Mircerson/AERQ/Code/v1/stm32customtargets/TARGET_STM32F4/TARGET_CORE2/PeripheralPinMaps.h

/* mbed Microcontroller Library
 *******************************************************************************
 * Copyright (c) 2018, STMicroelectronics
 * All rights reserved.
 *
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
 * THIS SOFTWARE IS PROVIDED BY THE COPYRIGHT HOLDERS AND CONTRIBUTORS "AS IS"
 * AND ANY EXPRESS OR IMPLIED WARRANTIES, INCLUDING, BUT NOT LIMITED TO, THE
 * IMPLIED WARRANTIES OF MERCHANTABILITY AND FITNESS FOR A PARTICULAR PURPOSE ARE
 * DISCLAIMED. IN NO EVENT SHALL THE COPYRIGHT HOLDER OR CONTRIBUTORS BE LIABLE
 * FOR ANY DIRECT, INDIRECT, INCIDENTAL, SPECIAL, EXEMPLARY, OR CONSEQUENTIAL
 * DAMAGES (INCLUDING, BUT NOT LIMITED TO, PROCUREMENT OF SUBSTITUTE GOODS OR
 * SERVICES; LOSS OF USE, DATA, OR PROFITS; OR BUSINESS INTERRUPTION) HOWEVER
 * CAUSED AND ON ANY THEORY OF LIABILITY, WHETHER IN CONTRACT, STRICT LIABILITY,
 * OR TORT (INCLUDING NEGLIGENCE OR OTHERWISE) ARISING IN ANY WAY OUT OF THE USE
 * OF THIS SOFTWARE, EVEN IF ADVISED OF THE POSSIBILITY OF SUCH DAMAGE.
 *******************************************************************************
 */

//==============================================================================
// Notes
//
// - The pins mentioned Px_y_ALTz are alternative possibilities which use other
//   HW peripheral instances. You can use them the same way as any other "normal"
//   pin (i.e. PwmOut pwm(PA_7_ALT0);). These pins are not displayed on the board
//   pinout image on mbed.org.
//
// - The pins which are connected to other components present on the board have
//   the comment "Connected to xxx". The pin function may not work properly in this
//   case. These pins may not be displayed on the board pinout image on mbed.org.
//   Please read the board reference manual and schematic for more information.
//
// - Warning: pins connected to the default STDIO_UART_TX and STDIO_UART_RX pins are commented
//   See https://os.mbed.com/teams/ST/wiki/STDIO for more information.
//
//==============================================================================

//FIXME: Comment out peripherals that cannot be used!
#ifndef MBED_PERIPHERALPINMAPS_H
#define MBED_PERIPHERALPINMAPS_H

#include "PinNamesTypes.h"
#include <mstd_cstddef>

//*** ADC ***

MSTD_CONSTEXPR_OBJ_11 const PinMap PinMap_ADC[] = {
    {PA_0,       ADC_1, STM_PIN_DATA_EXT(STM_MODE_ANALOG, GPIO_NOPULL, 0, 0, 0)}, // ADC1_IN0
    {PA_0_ALT0,  ADC_2, STM_PIN_DATA_EXT(STM_MODE_ANALOG, GPIO_NOPULL, 0, 0, 0)}, // ADC2_IN0
    {PA_0_ALT1,  ADC_3, STM_PIN_DATA_EXT(STM_MODE_ANALOG, GPIO_NOPULL, 0, 0, 0)}, // ADC3_IN0
    {PA_1,       ADC_1, STM_PIN_DATA_EXT(STM_MODE_ANALOG, GPIO_NOPULL, 0, 1, 0)}, // ADC1_IN1
    {PA_1_ALT0,  ADC_2, STM_PIN_DATA_EXT(STM_MODE_ANALOG, GPIO_NOPULL, 0, 1, 0)}, // ADC2_IN1
    {PA_1_ALT1,  ADC_3, STM_PIN_DATA_EXT(STM_MODE_ANALOG, GPIO_NOPULL, 0, 1, 0)}, // ADC3_IN1
    {PA_2,       ADC_1, STM_PIN_DATA_EXT(STM_MODE_ANALOG, GPIO_NOPULL, 0, 2, 0)}, // ADC1_IN2
    {PA_2_ALT0,  ADC_2, STM_PIN_DATA_EXT(STM_MODE_ANALOG, GPIO_NOPULL, 0, 2, 0)}, // ADC2_IN2
    {PA_2_ALT1,  ADC_3, STM_PIN_DATA_EXT(STM_MODE_ANALOG, GPIO_NOPULL, 0, 2, 0)}, // ADC3_IN2
    {PA_3,       ADC_1, STM_PIN_DATA_EXT(STM_MODE_ANALOG, GPIO_NOPULL, 0, 3, 0)}, // ADC1_IN3
    {PA_3_ALT0,  ADC_2, STM_PIN_DATA_EXT(STM_MODE_ANALOG, GPIO_NOPULL, 0, 3, 0)}, // ADC2_IN3
    {PA_3_ALT1,  ADC_3, STM_PIN_DATA_EXT(STM_MODE_ANALOG, GPIO_NOPULL, 0, 3, 0)}, // ADC3_IN3
    {PA_4,       ADC_1, STM_PIN_DATA_EXT(STM_MODE_ANALOG, GPIO_NOPULL, 0, 4, 0)}, // ADC1_IN4 
    {PA_4_ALT0,  ADC_2, STM_PIN_DATA_EXT(STM_MODE_ANALOG, GPIO_NOPULL, 0, 4, 0)}, // ADC2_IN4 
    {PA_5,       ADC_1, STM_PIN_DATA_EXT(STM_MODE_ANALOG, GPIO_NOPULL, 0, 5, 0)}, // ADC1_IN5 
    {PA_5_ALT0,  ADC_2, STM_PIN_DATA_EXT(STM_MODE_ANALOG, GPIO_NOPULL, 0, 5, 0)}, // ADC2_IN5 
    {PA_6,       ADC_1, STM_PIN_DATA_EXT(STM_MODE_ANALOG, GPIO_NOPULL, 0, 6, 0)}, // ADC1_IN6 
    {PA_6_ALT0,  ADC_2, STM_PIN_DATA_EXT(STM_MODE_ANALOG, GPIO_NOPULL, 0, 6, 0)}, // ADC2_IN6 
    {PA_7,       ADC_1, STM_PIN_DATA_EXT(STM_MODE_ANALOG, GPIO_NOPULL, 0, 7, 0)}, // ADC1_IN7 
    {PA_7_ALT0,  ADC_2, STM_PIN_DATA_EXT(STM_MODE_ANALOG, GPIO_NOPULL, 0, 7, 0)}, // ADC2_IN7 
    {PB_0,       ADC_1, STM_PIN_DATA_EXT(STM_MODE_ANALOG, GPIO_NOPULL, 0, 8, 0)}, // ADC1_IN8
    {PB_0_ALT0,  ADC_2, STM_PIN_DATA_EXT(STM_MODE_ANALOG, GPIO_NOPULL, 0, 8, 0)}, // ADC2_IN8
    {PB_1,       ADC_1, STM_PIN_DATA_EXT(STM_MODE_ANALOG, GPIO_NOPULL, 0, 9, 0)}, // ADC1_IN9
    {PB_1_ALT0,  ADC_2, STM_PIN_DATA_EXT(STM_MODE_ANALOG, GPIO_NOPULL, 0, 9, 0)}, // ADC2_IN9
    {PC_0,       ADC_1, STM_PIN_DATA_EXT(STM_MODE_ANALOG, GPIO_NOPULL, 0, 10, 0)}, // ADC1_IN10 
    {PC_0_ALT0,  ADC_2, STM_PIN_DATA_EXT(STM_MODE_ANALOG, GPIO_NOPULL, 0, 10, 0)}, // ADC2_IN10 
    {PC_0_ALT1,  ADC_3, STM_PIN_DATA_EXT(STM_MODE_ANALOG, GPIO_NOPULL, 0, 10, 0)}, // ADC3_IN10 
    {PC_1,       ADC_1, STM_PIN_DATA_EXT(STM_MODE_ANALOG, GPIO_NOPULL, 0, 11, 0)}, // ADC1_IN11
    {PC_1_ALT0,  ADC_2, STM_PIN_DATA_EXT(STM_MODE_ANALOG, GPIO_NOPULL, 0, 11, 0)}, // ADC2_IN11
    {PC_1_ALT1,  ADC_3, STM_PIN_DATA_EXT(STM_MODE_ANALOG, GPIO_NOPULL, 0, 11, 0)}, // ADC3_IN11
    {PC_2,       ADC_1, STM_PIN_DATA_EXT(STM_MODE_ANALOG, GPIO_NOPULL, 0, 12, 0)}, // ADC1_IN12
    {PC_2_ALT0,  ADC_2, STM_PIN_DATA_EXT(STM_MODE_ANALOG, GPIO_NOPULL, 0, 12, 0)}, // ADC2_IN12
    {PC_2_ALT1,  ADC_3, STM_PIN_DATA_EXT(STM_MODE_ANALOG, GPIO_NOPULL, 0, 12, 0)}, // ADC3_IN12
    {PC_3,       ADC_1, STM_PIN_DATA_EXT(STM_MODE_ANALOG, GPIO_NOPULL, 0, 13, 0)}, // ADC1_IN13 
    {PC_3_ALT0,  ADC_2, STM_PIN_DATA_EXT(STM_MODE_ANALOG, GPIO_NOPULL, 0, 13, 0)}, // ADC2_IN13 
    {PC_3_ALT1,  ADC_3, STM_PIN_DATA_EXT(STM_MODE_ANALOG, GPIO_NOPULL, 0, 13, 0)}, // ADC3_IN13 
    {PC_4,       ADC_1, STM_PIN_DATA_EXT(STM_MODE_ANALOG, GPIO_NOPULL, 0, 14, 0)}, // ADC1_IN14
    {PC_4_ALT0,  ADC_2, STM_PIN_DATA_EXT(STM_MODE_ANALOG, GPIO_NOPULL, 0, 14, 0)}, // ADC2_IN14
    {PC_5,       ADC_1, STM_PIN_DATA_EXT(STM_MODE_ANALOG, GPIO_NOPULL, 0, 15, 0)}, // ADC1_IN15
    {PC_5_ALT0,  ADC_2, STM_PIN_DATA_EXT(STM_MODE_ANALOG, GPIO_NOPULL, 0, 15, 0)}, // ADC2_IN15
    {PF_3,       ADC_3, STM_PIN_DATA_EXT(STM_MODE_ANALOG, GPIO_NOPULL, 0, 9, 0)}, // ADC3_IN9
    {PF_4,       ADC_3, STM_PIN_DATA_EXT(STM_MODE_ANALOG, GPIO_NOPULL, 0, 14, 0)}, // ADC3_IN14
    {PF_5,       ADC_3, STM_PIN_DATA_EXT(STM_MODE_ANALOG, GPIO_NOPULL, 0, 15, 0)}, // ADC3_IN15
    {PF_6,       ADC_3, STM_PIN_DATA_EXT(STM_MODE_ANALOG, GPIO_NOPULL, 0, 4, 0)}, // ADC3_IN4
    {PF_7,       ADC_3, STM_PIN_DATA_EXT(STM_MODE_ANALOG, GPIO_NOPULL, 0, 5, 0)}, // ADC3_IN5
    {PF_8,       ADC_3, STM_PIN_DATA_EXT(STM_MODE_ANALOG, GPIO_NOPULL, 0, 6, 0)}, // ADC3_IN6
    {PF_9,       ADC_3, STM_PIN_DATA_EXT(STM_MODE_ANALOG, GPIO_NOPULL, 0, 7, 0)}, // ADC3_IN7
    {PF_10,      ADC_3, STM_PIN_DATA_EXT(STM_MODE_ANALOG, GPIO_NOPULL, 0, 8, 0)}, // ADC3_IN8
    {NC, NC, 0}
};

MSTD_CONSTEXPR_OBJ_11 const PinMap PinMap_ADC_Internal[] = {
    {ADC_TEMP,   ADC_1,    STM_PIN_DATA_EXT(STM_MODE_ANALOG, GPIO_NOPULL, 0, 16, 0)},
    {ADC_VREF,   ADC_1,    STM_PIN_DATA_EXT(STM_MODE_ANALOG, GPIO_NOPULL, 0, 17, 0)},
    {ADC_VBAT,   ADC_1,    STM_PIN_DATA_EXT(STM_MODE_ANALOG, GPIO_NOPULL, 0, 18, 0)},
    {NC, NC, 0}
};

//*** DAC ***

MSTD_CONSTEXPR_OBJ_11 const PinMap PinMap_DAC[] = {
    {PA_4,       DAC_1, STM_PIN_DATA_EXT(STM_MODE_ANALOG, GPIO_NOPULL, 0, 1, 0)}, // DAC_OUT1 
    {PA_5,       DAC_1, STM_PIN_DATA_EXT(STM_MODE_ANALOG, GPIO_NOPULL, 0, 2, 0)}, // DAC_OUT2 
    {NC, NC, 0}
};

//*** I2C ***

MSTD_CONSTEXPR_OBJ_11 const PinMap PinMap_I2C_SDA[] = {
    {PB_7,       I2C_1, STM_PIN_DATA(STM_MODE_AF_OD, GPIO_NOPULL, GPIO_AF4_I2C1)},
    {PB_9,       I2C_1, STM_PIN_DATA(STM_MODE_AF_OD, GPIO_NOPULL, GPIO_AF4_I2C1)}, 
    {PB_11,      I2C_2, STM_PIN_DATA(STM_MODE_AF_OD, GPIO_NOPULL, GPIO_AF4_I2C2)},
    {PC_9,       I2C_3, STM_PIN_DATA(STM_MODE_AF_OD, GPIO_NOPULL, GPIO_AF4_I2C3)},
    {PF_0,       I2C_2, STM_PIN_DATA(STM_MODE_AF_OD, GPIO_NOPULL, GPIO_AF4_I2C2)},
    {NC, NC, 0}
};

MSTD_CONSTEXPR_OBJ_11 const PinMap PinMap_I2C_SCL[] = {
    {PA_8,       I2C_3, STM_PIN_DATA(STM_MODE_AF_OD, GPIO_NOPULL, GPIO_AF4_I2C3)},
    {PB_6,       I2C_1, STM_PIN_DATA(STM_MODE_AF_OD, GPIO_NOPULL, GPIO_AF4_I2C1)}, 
    {PB_8,       I2C_1, STM_PIN_DATA(STM_MODE_AF_OD, GPIO_NOPULL, GPIO_AF4_I2C1)},
    {PB_10,      I2C_2, STM_PIN_DATA(STM_MODE_AF_OD, GPIO_NOPULL, GPIO_AF4_I2C2)}, 
    {PF_1,       I2C_2, STM_PIN_DATA(STM_MODE_AF_OD, GPIO_NOPULL, GPIO_AF4_I2C2)}, 
    {NC, NC, 0}
};

//*** PWM ***

// TIM5 cannot be used because already used by the us_ticker
MSTD_CONSTEXPR_OBJ_11 const PinMap PinMap_PWM[] = {
    {PA_0,       PWM_2,  STM_PIN_DATA_EXT(STM_MODE_AF_PP, GPIO_PULLUP, GPIO_AF1_TIM2, 1, 0)}, // TIM2_CH1
//  {PA_0,       PWM_5,  STM_PIN_DATA_EXT(STM_MODE_AF_PP, GPIO_PULLUP, GPIO_AF2_TIM5, 1, 0)}, // TIM5_CH1
    {PA_1,       PWM_2,  STM_PIN_DATA_EXT(STM_MODE_AF_PP, GPIO_PULLUP, GPIO_AF1_TIM2, 2, 0)}, // TIM2_CH2
//  {PA_1,       PWM_5,  STM_PIN_DATA_EXT(STM_MODE_AF_PP, GPIO_PULLUP, GPIO_AF2_TIM5, 2, 0)}, // TIM5_CH2
    {PA_2,       PWM_2,  STM_PIN_DATA_EXT(STM_MODE_AF_PP, GPIO_PULLUP, GPIO_AF1_TIM2, 3, 0)}, // TIM2_CH3
//  {PA_2,       PWM_5,  STM_PIN_DATA_EXT(STM_MODE_AF_PP, GPIO_PULLUP, GPIO_AF2_TIM5, 3, 0)}, // TIM5_CH3
    {PA_2_ALT0,  PWM_9,  STM_PIN_DATA_EXT(STM_MODE_AF_PP, GPIO_PULLUP, GPIO_AF3_TIM9, 1, 0)}, // TIM9_CH1
    {PA_3,       PWM_2,  STM_PIN_DATA_EXT(STM_MODE_AF_PP, GPIO_PULLUP, GPIO_AF1_TIM2, 4, 0)}, // TIM2_CH4
//  {PA_3,       PWM_5,  STM_PIN_DATA_EXT(STM_MODE_AF_PP, GPIO_PULLUP, GPIO_AF2_TIM5, 4, 0)}, // TIM5_CH4
    {PA_3_ALT0,  PWM_9,  STM_PIN_DATA_EXT(STM_MODE_AF_PP, GPIO_PULLUP, GPIO_AF3_TIM9, 2, 0)}, // TIM9_CH2
    {PA_5,       PWM_2,  STM_PIN_DATA_EXT(STM_MODE_AF_PP, GPIO_PULLUP, GPIO_AF1_TIM2, 1, 0)}, // TIM2_CH1 
    {PA_5_ALT0,  PWM_8,  STM_PIN_DATA_EXT(STM_MODE_AF_PP, GPIO_PULLUP, GPIO_AF3_TIM8, 1, 1)}, // TIM8_CH1N 
    {PA_6,       PWM_3,  STM_PIN_DATA_EXT(STM_MODE_AF_PP, GPIO_PULLUP, GPIO_AF2_TIM3, 1, 0)}, // TIM3_CH1 
    {PA_6_ALT0,  PWM_13, STM_PIN_DATA_EXT(STM_MODE_AF_PP, GPIO_PULLUP, GPIO_AF9_TIM13, 1, 0)}, // TIM13_CH1 
    {PA_7,       PWM_1,  STM_PIN_DATA_EXT(STM_MODE_AF_PP, GPIO_PULLUP, GPIO_AF1_TIM1, 1, 1)}, // TIM1_CH1N 
    {PA_7_ALT0,  PWM_3,  STM_PIN_DATA_EXT(STM_MODE_AF_PP, GPIO_PULLUP, GPIO_AF2_TIM3, 2, 0)}, // TIM3_CH2 
    {PA_7_ALT1,  PWM_8,  STM_PIN_DATA_EXT(STM_MODE_AF_PP, GPIO_PULLUP, GPIO_AF3_TIM8, 1, 1)}, // TIM8_CH1N 
    {PA_7_ALT2,  PWM_14, STM_PIN_DATA_EXT(STM_MODE_AF_PP, GPIO_PULLUP, GPIO_AF9_TIM14, 1, 0)}, // TIM14_CH1 
    {PA_8,       PWM_1,  STM_PIN_DATA_EXT(STM_MODE_AF_PP, GPIO_PULLUP, GPIO_AF1_TIM1, 1, 0)}, // TIM1_CH1
    {PA_9,       PWM_1,  STM_PIN_DATA_EXT(STM_MODE_AF_PP, GPIO_PULLUP, GPIO_AF1_TIM1, 2, 0)}, // TIM1_CH2 
    {PA_10,      PWM_1,  STM_PIN_DATA_EXT(STM_MODE_AF_PP, GPIO_PULLUP, GPIO_AF1_TIM1, 3, 0)}, // TIM1_CH3 
    {PA_11,      PWM_1,  STM_PIN_DATA_EXT(STM_MODE_AF_PP, GPIO_PULLUP, GPIO_AF1_TIM1, 4, 0)}, // TIM1_CH4 
    {PA_15,      PWM_2,  STM_PIN_DATA_EXT(STM_MODE_AF_PP, GPIO_PULLUP, GPIO_AF1_TIM2, 1, 0)}, // TIM2_CH1
    {PB_0,       PWM_1,  STM_PIN_DATA_EXT(STM_MODE_AF_PP, GPIO_PULLUP, GPIO_AF1_TIM1, 2, 1)}, // TIM1_CH2N
    {PB_0_ALT0,  PWM_3,  STM_PIN_DATA_EXT(STM_MODE_AF_PP, GPIO_PULLUP, GPIO_AF2_TIM3, 3, 0)}, // TIM3_CH3
    {PB_0_ALT1,  PWM_8,  STM_PIN_DATA_EXT(STM_MODE_AF_PP, GPIO_PULLUP, GPIO_AF3_TIM8, 2, 1)}, // TIM8_CH2N
    {PB_1,       PWM_1,  STM_PIN_DATA_EXT(STM_MODE_AF_PP, GPIO_PULLUP, GPIO_AF1_TIM1, 3, 1)}, // TIM1_CH3N
    {PB_1_ALT0,  PWM_3,  STM_PIN_DATA_EXT(STM_MODE_AF_PP, GPIO_PULLUP, GPIO_AF2_TIM3, 4, 0)}, // TIM3_CH4
    {PB_1_ALT1,  PWM_8,  STM_PIN_DATA_EXT(STM_MODE_AF_PP, GPIO_PULLUP, GPIO_AF3_TIM8, 3, 1)}, // TIM8_CH3N
    {PB_3,       PWM_2,  STM_PIN_DATA_EXT(STM_MODE_AF_PP, GPIO_PULLUP, GPIO_AF1_TIM2, 2, 0)}, // TIM2_CH2 
    {PB_4,       PWM_3,  STM_PIN_DATA_EXT(STM_MODE_AF_PP, GPIO_PULLUP, GPIO_AF2_TIM3, 1, 0)}, // TIM3_CH1
    {PB_5,       PWM_3,  STM_PIN_DATA_EXT(STM_MODE_AF_PP, GPIO_PULLUP, GPIO_AF2_TIM3, 2, 0)}, // TIM3_CH2
    {PB_6,       PWM_4,  STM_PIN_DATA_EXT(STM_MODE_AF_PP, GPIO_PULLUP, GPIO_AF2_TIM4, 1, 0)}, // TIM4_CH1 
    {PB_7,       PWM_4,  STM_PIN_DATA_EXT(STM_MODE_AF_PP, GPIO_PULLUP, GPIO_AF2_TIM4, 2, 0)}, // TIM4_CH2
    {PB_8,       PWM_4,  STM_PIN_DATA_EXT(STM_MODE_AF_PP, GPIO_PULLUP, GPIO_AF2_TIM4, 3, 0)}, // TIM4_CH3
    {PB_8_ALT0,  PWM_10, STM_PIN_DATA_EXT(STM_MODE_AF_PP, GPIO_PULLUP, GPIO_AF3_TIM10, 1, 0)}, // TIM10_CH1
    {PB_9,       PWM_4,  STM_PIN_DATA_EXT(STM_MODE_AF_PP, GPIO_PULLUP, GPIO_AF2_TIM4, 4, 0)}, // TIM4_CH4 
    {PB_9_ALT0,  PWM_11, STM_PIN_DATA_EXT(STM_MODE_AF_PP, GPIO_PULLUP, GPIO_AF3_TIM11, 1, 0)}, // TIM11_CH1 
    {PB_10,      PWM_2,  STM_PIN_DATA_EXT(STM_MODE_AF_PP, GPIO_PULLUP, GPIO_AF1_TIM2, 3, 0)}, // TIM2_CH3 
    {PB_11,      PWM_2,  STM_PIN_DATA_EXT(STM_MODE_AF_PP, GPIO_PULLUP, GPIO_AF1_TIM2, 4, 0)}, // TIM2_CH4
    {PB_13,      PWM_1,  STM_PIN_DATA_EXT(STM_MODE_AF_PP, GPIO_PULLUP, GPIO_AF1_TIM1, 1, 1)}, // TIM1_CH1N
    {PB_14,      PWM_1,  STM_PIN_DATA_EXT(STM_MODE_AF_PP, GPIO_PULLUP, GPIO_AF1_TIM1, 2, 1)}, // TIM1_CH2N
    {PB_14_ALT0, PWM_8,  STM_PIN_DATA_EXT(STM_MODE_AF_PP, GPIO_PULLUP, GPIO_AF3_TIM8, 2, 1)}, // TIM8_CH2N
    {PB_14_ALT1, PWM_12, STM_PIN_DATA_EXT(STM_MODE_AF_PP, GPIO_PULLUP, GPIO_AF9_TIM12, 1, 0)}, // TIM12_CH1
    {PB_15,      PWM_1,  STM_PIN_DATA_EXT(STM_MODE_AF_PP, GPIO_PULLUP, GPIO_AF1_TIM1, 3, 1)}, // TIM1_CH3N
    {PB_15_ALT0, PWM_8,  STM_PIN_DATA_EXT(STM_MODE_AF_PP, GPIO_PULLUP, GPIO_AF3_TIM8, 3, 1)}, // TIM8_CH3N
    {PB_15_ALT1, PWM_12, STM_PIN_DATA_EXT(STM_MODE_AF_PP, GPIO_PULLUP, GPIO_AF9_TIM12, 2, 0)}, // TIM12_CH2
    {PC_6,       PWM_3,  STM_PIN_DATA_EXT(STM_MODE_AF_PP, GPIO_PULLUP, GPIO_AF2_TIM3, 1, 0)}, // TIM3_CH1
    {PC_6_ALT0,  PWM_8,  STM_PIN_DATA_EXT(STM_MODE_AF_PP, GPIO_PULLUP, GPIO_AF3_TIM8, 1, 0)}, // TIM8_CH1
    {PC_7,       PWM_3,  STM_PIN_DATA_EXT(STM_MODE_AF_PP, GPIO_PULLUP, GPIO_AF2_TIM3, 2, 0)}, // TIM3_CH2 
    {PC_7_ALT0,  PWM_8,  STM_PIN_DATA_EXT(STM_MODE_AF_PP, GPIO_PULLUP, GPIO_AF3_TIM8, 2, 0)}, // TIM8_CH2 
    {PC_8,       PWM_3,  STM_PIN_DATA_EXT(STM_MODE_AF_PP, GPIO_PULLUP, GPIO_AF2_TIM3, 3, 0)}, // TIM3_CH3
    {PC_8_ALT0,  PWM_8,  STM_PIN_DATA_EXT(STM_MODE_AF_PP, GPIO_PULLUP, GPIO_AF3_TIM8, 3, 0)}, // TIM8_CH3
    {PC_9,       PWM_3,  STM_PIN_DATA_EXT(STM_MODE_AF_PP, GPIO_PULLUP, GPIO_AF2_TIM3, 4, 0)}, // TIM3_CH4
    {PC_9_ALT0,  PWM_8,  STM_PIN_DATA_EXT(STM_MODE_AF_PP, GPIO_PULLUP, GPIO_AF3_TIM8, 4, 0)}, // TIM8_CH4
    {PD_12,      PWM_4,  STM_PIN_DATA_EXT(STM_MODE_AF_PP, GPIO_PULLUP, GPIO_AF2_TIM4, 1, 0)}, // TIM4_CH1 
    {PD_13,      PWM_4,  STM_PIN_DATA_EXT(STM_MODE_AF_PP, GPIO_PULLUP, GPIO_AF2_TIM4, 2, 0)}, // TIM4_CH2 
    {PD_14,      PWM_4,  STM_PIN_DATA_EXT(STM_MODE_AF_PP, GPIO_PULLUP, GPIO_AF2_TIM4, 3, 0)}, // TIM4_CH3 
    {PD_15,      PWM_4,  STM_PIN_DATA_EXT(STM_MODE_AF_PP, GPIO_PULLUP, GPIO_AF2_TIM4, 4, 0)}, // TIM4_CH4 
    {PE_5,       PWM_9,  STM_PIN_DATA_EXT(STM_MODE_AF_PP, GPIO_PULLUP, GPIO_AF3_TIM9, 1, 0)}, // TIM9_CH1
    {PE_6,       PWM_9,  STM_PIN_DATA_EXT(STM_MODE_AF_PP, GPIO_PULLUP, GPIO_AF3_TIM9, 2, 0)}, // TIM9_CH2
    {PE_8,       PWM_1,  STM_PIN_DATA_EXT(STM_MODE_AF_PP, GPIO_PULLUP, GPIO_AF1_TIM1, 1, 1)}, // TIM1_CH1N
    {PE_9,       PWM_1,  STM_PIN_DATA_EXT(STM_MODE_AF_PP, GPIO_PULLUP, GPIO_AF1_TIM1, 1, 0)}, // TIM1_CH1
    {PE_10,      PWM_1,  STM_PIN_DATA_EXT(STM_MODE_AF_PP, GPIO_PULLUP, GPIO_AF1_TIM1, 2, 1)}, // TIM1_CH2N
    {PE_11,      PWM_1,  STM_PIN_DATA_EXT(STM_MODE_AF_PP, GPIO_PULLUP, GPIO_AF1_TIM1, 2, 0)}, // TIM1_CH2
    {PE_12,      PWM_1,  STM_PIN_DATA_EXT(STM_MODE_AF_PP, GPIO_PULLUP, GPIO_AF1_TIM1, 3, 1)}, // TIM1_CH3N
    {PE_13,      PWM_1,  STM_PIN_DATA_EXT(STM_MODE_AF_PP, GPIO_PULLUP, GPIO_AF1_TIM1, 3, 0)}, // TIM1_CH3
    {PE_14,      PWM_1,  STM_PIN_DATA_EXT(STM_MODE_AF_PP, GPIO_PULLUP, GPIO_AF1_TIM1, 4, 0)}, // TIM1_CH4
    {PF_6,       PWM_10, STM_PIN_DATA_EXT(STM_MODE_AF_PP, GPIO_PULLUP, GPIO_AF3_TIM10, 1, 0)}, // TIM10_CH1
    {PF_7,       PWM_11, STM_PIN_DATA_EXT(STM_MODE_AF_PP, GPIO_PULLUP, GPIO_AF3_TIM11, 1, 0)}, // TIM11_CH1
    {PF_8,       PWM_13, STM_PIN_DATA_EXT(STM_MODE_AF_PP, GPIO_PULLUP, GPIO_AF9_TIM13, 1, 0)}, // TIM13_CH1
    {PF_9,       PWM_14, STM_PIN_DATA_EXT(STM_MODE_AF_PP, GPIO_PULLUP, GPIO_AF9_TIM14, 1, 0)}, // TIM14_CH1
    {NC, NC, 0}
};

//*** SERIAL ***

MSTD_CONSTEXPR_OBJ_11 const PinMap PinMap_UART_TX[] = {
    {PA_0,       UART_4,  STM_PIN_DATA(STM_MODE_AF_PP, GPIO_PULLUP, GPIO_AF8_UART4)}, 
    {PA_2,       UART_2,  STM_PIN_DATA(STM_MODE_AF_PP, GPIO_PULLUP, GPIO_AF7_USART2)},
    {PA_9,       UART_1,  STM_PIN_DATA(STM_MODE_AF_PP, GPIO_PULLUP, GPIO_AF7_USART1)}, 
    {PB_6,       UART_1,  STM_PIN_DATA(STM_MODE_AF_PP, GPIO_PULLUP, GPIO_AF7_USART1)}, 
    {PB_10,      UART_3,  STM_PIN_DATA(STM_MODE_AF_PP, GPIO_PULLUP, GPIO_AF7_USART3)}, 
    {PC_6,       UART_6,  STM_PIN_DATA(STM_MODE_AF_PP, GPIO_PULLUP, GPIO_AF8_USART6)},
    {PC_10,      UART_3,  STM_PIN_DATA(STM_MODE_AF_PP, GPIO_PULLUP, GPIO_AF7_USART3)}, 
    {PC_10_ALT0, UART_4,  STM_PIN_DATA(STM_MODE_AF_PP, GPIO_PULLUP, GPIO_AF8_UART4)}, 
    {PC_12,      UART_5,  STM_PIN_DATA(STM_MODE_AF_PP, GPIO_PULLUP, GPIO_AF8_UART5)}, 
    {PD_5,       UART_2,  STM_PIN_DATA(STM_MODE_AF_PP, GPIO_PULLUP, GPIO_AF7_USART2)}, 
    {PD_8,       UART_3,  STM_PIN_DATA(STM_MODE_AF_PP, GPIO_PULLUP, GPIO_AF7_USART3)},
    {PG_14,      UART_6,  STM_PIN_DATA(STM_MODE_AF_PP, GPIO_PULLUP, GPIO_AF8_USART6)},
    {NC, NC, 0}
};

MSTD_CONSTEXPR_OBJ_11 const PinMap PinMap_UART_RX[] = {
    {PA_1,       UART_4,  STM_PIN_DATA(STM_MODE_AF_PP, GPIO_PULLUP, GPIO_AF8_UART4)},
    {PA_3,       UART_2,  STM_PIN_DATA(STM_MODE_AF_PP, GPIO_PULLUP, GPIO_AF7_USART2)},
    {PA_10,      UART_1,  STM_PIN_DATA(STM_MODE_AF_PP, GPIO_PULLUP, GPIO_AF7_USART1)}, 
    {PB_7,       UART_1,  STM_PIN_DATA(STM_MODE_AF_PP, GPIO_PULLUP, GPIO_AF7_USART1)},
    {PB_11,      UART_3,  STM_PIN_DATA(STM_MODE_AF_PP, GPIO_PULLUP, GPIO_AF7_USART3)},
    {PC_7,       UART_6,  STM_PIN_DATA(STM_MODE_AF_PP, GPIO_PULLUP, GPIO_AF8_USART6)}, 
    {PC_11,      UART_3,  STM_PIN_DATA(STM_MODE_AF_PP, GPIO_PULLUP, GPIO_AF7_USART3)},
    {PC_11_ALT0, UART_4,  STM_PIN_DATA(STM_MODE_AF_PP, GPIO_PULLUP, GPIO_AF8_UART4)},
    {PD_2,       UART_5,  STM_PIN_DATA(STM_MODE_AF_PP, GPIO_PULLUP, GPIO_AF8_UART5)},
    {PD_6,       UART_2,  STM_PIN_DATA(STM_MODE_AF_PP, GPIO_PULLUP, GPIO_AF7_USART2)},
    {PD_9,       UART_3,  STM_PIN_DATA(STM_MODE_AF_PP, GPIO_PULLUP, GPIO_AF7_USART3)},
    {PG_9,       UART_6,  STM_PIN_DATA(STM_MODE_AF_PP, GPIO_PULLUP, GPIO_AF8_USART6)},
    {NC, NC, 0}
};

MSTD_CONSTEXPR_OBJ_11 const PinMap PinMap_UART_RTS[] = {
    {PA_1,       UART_2,  STM_PIN_DATA(STM_MODE_AF_PP, GPIO_PULLUP, GPIO_AF7_USART2)},
    {PA_12,      UART_1,  STM_PIN_DATA(STM_MODE_AF_PP, GPIO_PULLUP, GPIO_AF7_USART1)}, 
    {PB_14,      UART_3,  STM_PIN_DATA(STM_MODE_AF_PP, GPIO_PULLUP, GPIO_AF7_USART3)},
    {PD_4,       UART_2,  STM_PIN_DATA(STM_MODE_AF_PP, GPIO_PULLUP, GPIO_AF7_USART2)}, 
    {PD_12,      UART_3,  STM_PIN_DATA(STM_MODE_AF_PP, GPIO_PULLUP, GPIO_AF7_USART3)}, 
    {PG_8,       UART_6,  STM_PIN_DATA(STM_MODE_AF_PP, GPIO_PULLUP, GPIO_AF8_USART6)},
    {PG_12,      UART_6,  STM_PIN_DATA(STM_MODE_AF_PP, GPIO_PULLUP, GPIO_AF8_USART6)},
    {NC, NC, 0}
};

MSTD_CONSTEXPR_OBJ_11 const PinMap PinMap_UART_CTS[] = {
    {PA_0,       UART_2,  STM_PIN_DATA(STM_MODE_AF_PP, GPIO_PULLUP, GPIO_AF7_USART2)}, 
    {PA_11,      UART_1,  STM_PIN_DATA(STM_MODE_AF_PP, GPIO_PULLUP, GPIO_AF7_USART1)}, 
    {PB_13,      UART_3,  STM_PIN_DATA(STM_MODE_AF_PP, GPIO_PULLUP, GPIO_AF7_USART3)},
    {PD_3,       UART_2,  STM_PIN_DATA(STM_MODE_AF_PP, GPIO_PULLUP, GPIO_AF7_USART2)},
    {PD_11,      UART_3,  STM_PIN_DATA(STM_MODE_AF_PP, GPIO_PULLUP, GPIO_AF7_USART3)},
    {PG_13,      UART_6,  STM_PIN_DATA(STM_MODE_AF_PP, GPIO_PULLUP, GPIO_AF8_USART6)},
    {PG_15,      UART_6,  STM_PIN_DATA(STM_MODE_AF_PP, GPIO_PULLUP, GPIO_AF8_USART6)},
    {NC, NC, 0}
};

//*** SPI ***

MSTD_CONSTEXPR_OBJ_11 const PinMap PinMap_SPI_MOSI[] = {
    {PA_7,       SPI_1, STM_PIN_DATA(STM_MODE_AF_PP, GPIO_NOPULL, GPIO_AF5_SPI1)}, 
    {PB_5,       SPI_1, STM_PIN_DATA(STM_MODE_AF_PP, GPIO_NOPULL, GPIO_AF5_SPI1)},
    {PB_5_ALT0,  SPI_3, STM_PIN_DATA(STM_MODE_AF_PP, GPIO_NOPULL, GPIO_AF6_SPI3)},
    {PB_15,      SPI_2, STM_PIN_DATA(STM_MODE_AF_PP, GPIO_NOPULL, GPIO_AF5_SPI2)},
    {PC_3,       SPI_2, STM_PIN_DATA(STM_MODE_AF_PP, GPIO_NOPULL, GPIO_AF5_SPI2)}, 
    {PC_12,      SPI_3, STM_PIN_DATA(STM_MODE_AF_PP, GPIO_NOPULL, GPIO_AF6_SPI3)}, 
    {NC, NC, 0}
};

MSTD_CONSTEXPR_OBJ_11 const PinMap PinMap_SPI_MISO[] = {
    {PA_6,       SPI_1, STM_PIN_DATA(STM_MODE_AF_PP, GPIO_NOPULL, GPIO_AF5_SPI1)}, 
    {PB_4,       SPI_1, STM_PIN_DATA(STM_MODE_AF_PP, GPIO_NOPULL, GPIO_AF5_SPI1)},
    {PB_4_ALT0,  SPI_3, STM_PIN_DATA(STM_MODE_AF_PP, GPIO_NOPULL, GPIO_AF6_SPI3)},
    {PB_14,      SPI_2, STM_PIN_DATA(STM_MODE_AF_PP, GPIO_NOPULL, GPIO_AF5_SPI2)},
    {PC_2,       SPI_2, STM_PIN_DATA(STM_MODE_AF_PP, GPIO_NOPULL, GPIO_AF5_SPI2)},
    {PC_11,      SPI_3, STM_PIN_DATA(STM_MODE_AF_PP, GPIO_NOPULL, GPIO_AF6_SPI3)},
    {NC, NC, 0}
};

MSTD_CONSTEXPR_OBJ_11 const PinMap PinMap_SPI_SCLK[] = {
    {PA_5,       SPI_1, STM_PIN_DATA(STM_MODE_AF_PP, GPIO_NOPULL, GPIO_AF5_SPI1)}, 
    {PB_3,       SPI_1, STM_PIN_DATA(STM_MODE_AF_PP, GPIO_NOPULL, GPIO_AF5_SPI1)}, 
    {PB_3_ALT0,  SPI_3, STM_PIN_DATA(STM_MODE_AF_PP, GPIO_NOPULL, GPIO_AF6_SPI3)}, 
    {PB_10,      SPI_2, STM_PIN_DATA(STM_MODE_AF_PP, GPIO_NOPULL, GPIO_AF5_SPI2)}, 
    {PB_13,      SPI_2, STM_PIN_DATA(STM_MODE_AF_PP, GPIO_NOPULL, GPIO_AF5_SPI2)},
    {PC_10,      SPI_3, STM_PIN_DATA(STM_MODE_AF_PP, GPIO_NOPULL, GPIO_AF6_SPI3)}, 
    {NC, NC, 0}
};

MSTD_CONSTEXPR_OBJ_11 const PinMap PinMap_SPI_SSEL[] = {
    {PA_4,       SPI_1, STM_PIN_DATA(STM_MODE_AF_PP, GPIO_NOPULL, GPIO_AF5_SPI1)}, 
    {PA_4_ALT0,  SPI_3, STM_PIN_DATA(STM_MODE_AF_PP, GPIO_NOPULL, GPIO_AF6_SPI3)}, 
    {PA_15,      SPI_1, STM_PIN_DATA(STM_MODE_AF_PP, GPIO_NOPULL, GPIO_AF5_SPI1)},
    {PA_15_ALT0, SPI_3, STM_PIN_DATA(STM_MODE_AF_PP, GPIO_NOPULL, GPIO_AF6_SPI3)},
    {PB_9,       SPI_2, STM_PIN_DATA(STM_MODE_AF_PP, GPIO_NOPULL, GPIO_AF5_SPI2)}, 
    {PB_12,      SPI_2, STM_PIN_DATA(STM_MODE_AF_PP, GPIO_NOPULL, GPIO_AF5_SPI2)},
    {NC, NC, 0}
};

//*** CAN ***

MSTD_CONSTEXPR_OBJ_11 const PinMap PinMap_CAN_RD[] = {
    {PA_11,      CAN_1, STM_PIN_DATA(STM_MODE_AF_PP, GPIO_NOPULL, GPIO_AF9_CAN1)}, 
    {PB_5,       CAN_2, STM_PIN_DATA(STM_MODE_AF_PP, GPIO_NOPULL, GPIO_AF9_CAN2)},
    {PB_8,       CAN_1, STM_PIN_DATA(STM_MODE_AF_PP, GPIO_NOPULL, GPIO_AF9_CAN1)},
    {PB_12,      CAN_2, STM_PIN_DATA(STM_MODE_AF_PP, GPIO_NOPULL, GPIO_AF9_CAN2)},
    {PD_0,       CAN_1, STM_PIN_DATA(STM_MODE_AF_PP, GPIO_NOPULL, GPIO_AF9_CAN1)},
    {NC, NC, 0}
};

MSTD_CONSTEXPR_OBJ_11 const PinMap PinMap_CAN_TD[] = {
    {PA_12,      CAN_1, STM_PIN_DATA(STM_MODE_AF_PP, GPIO_NOPULL, GPIO_AF9_CAN1)}, 
    {PB_6,       CAN_2, STM_PIN_DATA(STM_MODE_AF_PP, GPIO_NOPULL, GPIO_AF9_CAN2)}, 
    {PB_9,       CAN_1, STM_PIN_DATA(STM_MODE_AF_PP, GPIO_NOPULL, GPIO_AF9_CAN1)}, 
    {PB_13,      CAN_2, STM_PIN_DATA(STM_MODE_AF_PP, GPIO_NOPULL, GPIO_AF9_CAN2)},
    {PD_1,       CAN_1, STM_PIN_DATA(STM_MODE_AF_PP, GPIO_NOPULL, GPIO_AF9_CAN1)},
    {NC, NC, 0}
};

#endif /* MBED_PERIPHERALPINMAPS_H */
