Mircerson/AERQ/Code/v1/stm32customtargets/TARGET_STM32L0/TARGET_MTB_MURATA_ABZ/PeripheralPins.c

/* mbed Microcontroller Library
 * SPDX-License-Identifier: BSD-3-Clause
 ******************************************************************************
 *
 * Copyright (c) 2016-2021 STMicroelectronics.
 * All rights reserved.
 *
 * This software component is licensed by ST under BSD 3-Clause license,
 * the "License"; You may not use this file except in compliance with the
 * License. You may obtain a copy of the License at:
 *                        opensource.org/licenses/BSD-3-Clause
 *
 ******************************************************************************
 *
 * Automatically generated from STM32CubeMX/db/mcu/STM32L082CZUx.xml
 */

#include "PeripheralPins.h"
#include "mbed_toolchain.h"

//==============================================================================
// Notes
//
// - The pins mentioned Px_y_ALTz are alternative possibilities which use other
//   HW peripheral instances. You can use them the same way as any other "normal"
//   pin (i.e. PwmOut pwm(PA_7_ALT0);). These pins are not displayed on the board
//   pinout image on mbed.org.
//
// - The pins which are connected to other components present on the board have
//   the comment "Connected to xxx". The pin function may not work properly in this
//   case. These pins may not be displayed on the board pinout image on mbed.org.
//   Please read the board reference manual and schematic for more information.
//
// - Warning: pins connected to the default STDIO_UART_TX and STDIO_UART_RX pins are commented
//   See https://os.mbed.com/teams/ST/wiki/STDIO for more information.
//
//==============================================================================


//*** ADC ***

MBED_WEAK const PinMap PinMap_ADC[] = {
    {PA_0, ADC_1, STM_PIN_DATA_EXT(STM_MODE_ANALOG, GPIO_NOPULL, 0, 0, 0)}, // BLUE-LED
    {PA_2, ADC_1, STM_PIN_DATA_EXT(STM_MODE_ANALOG, GPIO_NOPULL, 0, 2, 0)}, // POT
    {PA_3, ADC_1, STM_PIN_DATA_EXT(STM_MODE_ANALOG, GPIO_NOPULL, 0, 3, 0)}, // BUTTON
    {PA_4, ADC_1, STM_PIN_DATA_EXT(STM_MODE_ANALOG, GPIO_NOPULL, 0, 4, 0)}, // RED-LED
    {PA_5, ADC_1, STM_PIN_DATA_EXT(STM_MODE_ANALOG, GPIO_NOPULL, 0, 5, 0)}, // GREEN-LED
    {NC,   NC,    0}
};

MBED_WEAK const PinMap PinMap_ADC_Internal[] = {
    {ADC_VREF,   ADC_1,    STM_PIN_DATA_EXT(STM_MODE_ANALOG, GPIO_NOPULL, 0, 17, 0)}, // ADC_IN17 // VREFINT
    {ADC_TEMP,   ADC_1,    STM_PIN_DATA_EXT(STM_MODE_ANALOG, GPIO_NOPULL, 0, 18, 0)}, // ADC_IN18 // VSENSE
    {NC,       NC,    0}
};

//*** DAC ***

MBED_WEAK const PinMap PinMap_DAC[] = {
    {PA_4, DAC_1, STM_PIN_DATA_EXT(STM_MODE_ANALOG, GPIO_NOPULL, 0, 1, 0)}, // RED-LED
    {PA_5, DAC_1, STM_PIN_DATA_EXT(STM_MODE_ANALOG, GPIO_NOPULL, 0, 2, 0)}, // GREEN-LED
    {NC,   NC,    0}
};

//*** I2C ***

MBED_WEAK const PinMap PinMap_I2C_SDA[] = {
    {PA_10, I2C_1, STM_PIN_DATA(STM_MODE_AF_OD, GPIO_NOPULL, GPIO_AF6_I2C1)},
    {PB_7,  I2C_1, STM_PIN_DATA(STM_MODE_AF_OD, GPIO_NOPULL, GPIO_AF1_I2C1)},
    {PB_9,  I2C_1, STM_PIN_DATA(STM_MODE_AF_OD, GPIO_NOPULL, GPIO_AF4_I2C1)}, // SDA
    {PB_14, I2C_2, STM_PIN_DATA(STM_MODE_AF_OD, GPIO_NOPULL, GPIO_AF5_I2C2)},
    {NC,    NC,    0}
};

MBED_WEAK const PinMap PinMap_I2C_SCL[] = {
    {PA_9,  I2C_1, STM_PIN_DATA(STM_MODE_AF_OD, GPIO_NOPULL, GPIO_AF6_I2C1)},
    {PB_6,  I2C_1, STM_PIN_DATA(STM_MODE_AF_OD, GPIO_NOPULL, GPIO_AF1_I2C1)},
    {PB_8,  I2C_1, STM_PIN_DATA(STM_MODE_AF_OD, GPIO_NOPULL, GPIO_AF4_I2C1)}, // SCL
    {PB_13, I2C_2, STM_PIN_DATA(STM_MODE_AF_OD, GPIO_NOPULL, GPIO_AF5_I2C2)},
    {NC,    NC,    0}
};

//*** PWM ***

// TIM21 cannot be used because already used by the us_ticker
// (update us_ticker_data.h file if another timer is chosen)
MBED_WEAK const PinMap PinMap_PWM[] = {
    {PA_0,       PWM_2,  STM_PIN_DATA_EXT(STM_MODE_AF_PP, GPIO_NOPULL, GPIO_AF2_TIM2, 1, 0)}, // TIM2_CH1
    {PA_1,       PWM_2,  STM_PIN_DATA_EXT(STM_MODE_AF_PP, GPIO_NOPULL, GPIO_AF2_TIM2, 2, 0)}, // TIM2_CH2
    {PA_2,       PWM_2,  STM_PIN_DATA_EXT(STM_MODE_AF_PP, GPIO_NOPULL, GPIO_AF2_TIM2, 3, 0)}, // TIM2_CH3
//  {PA_2,       PWM_21, STM_PIN_DATA_EXT(STM_MODE_AF_PP, GPIO_NOPULL, GPIO_AF0_TIM21, 1, 0)}, // TIM21_CH1
    {PA_3,       PWM_2,  STM_PIN_DATA_EXT(STM_MODE_AF_PP, GPIO_NOPULL, GPIO_AF2_TIM2, 4, 0)}, // TIM2_CH4
//  {PA_3,       PWM_21, STM_PIN_DATA_EXT(STM_MODE_AF_PP, GPIO_NOPULL, GPIO_AF0_TIM21, 2, 0)}, // TIM21_CH2
    {PA_5,       PWM_2,  STM_PIN_DATA_EXT(STM_MODE_AF_PP, GPIO_NOPULL, GPIO_AF5_TIM2, 1, 0)}, // TIM2_CH1
    {PA_6,       PWM_3,  STM_PIN_DATA_EXT(STM_MODE_AF_PP, GPIO_NOPULL, GPIO_AF2_TIM3, 1, 0)}, // TIM3_CH1
    {PA_6_ALT0,  PWM_22, STM_PIN_DATA_EXT(STM_MODE_AF_PP, GPIO_NOPULL, GPIO_AF5_TIM22, 1, 0)}, // TIM22_CH1
    {PA_7,       PWM_3,  STM_PIN_DATA_EXT(STM_MODE_AF_PP, GPIO_NOPULL, GPIO_AF2_TIM3, 2, 0)}, // TIM3_CH2
    {PA_7_ALT0,  PWM_22, STM_PIN_DATA_EXT(STM_MODE_AF_PP, GPIO_NOPULL, GPIO_AF5_TIM22, 2, 0)}, // TIM22_CH2
    {PA_15,      PWM_2,  STM_PIN_DATA_EXT(STM_MODE_AF_PP, GPIO_NOPULL, GPIO_AF5_TIM2, 1, 0)}, // TIM2_CH1
    {PB_0,       PWM_3,  STM_PIN_DATA_EXT(STM_MODE_AF_PP, GPIO_NOPULL, GPIO_AF2_TIM3, 3, 0)}, // TIM3_CH3
    {PB_1,       PWM_3,  STM_PIN_DATA_EXT(STM_MODE_AF_PP, GPIO_NOPULL, GPIO_AF2_TIM3, 4, 0)}, // TIM3_CH4
    {PB_3,       PWM_2,  STM_PIN_DATA_EXT(STM_MODE_AF_PP, GPIO_NOPULL, GPIO_AF2_TIM2, 2, 0)}, // TIM2_CH2
    {PB_4,       PWM_3,  STM_PIN_DATA_EXT(STM_MODE_AF_PP, GPIO_NOPULL, GPIO_AF2_TIM3, 1, 0)}, // TIM3_CH1
    {PB_4_ALT0,  PWM_22, STM_PIN_DATA_EXT(STM_MODE_AF_PP, GPIO_NOPULL, GPIO_AF4_TIM22, 1, 0)}, // TIM22_CH1
    {PB_5,       PWM_3,  STM_PIN_DATA_EXT(STM_MODE_AF_PP, GPIO_NOPULL, GPIO_AF4_TIM3, 2, 0)}, // TIM3_CH2
    {PB_5_ALT0,  PWM_22, STM_PIN_DATA_EXT(STM_MODE_AF_PP, GPIO_NOPULL, GPIO_AF4_TIM22, 2, 0)}, // TIM22_CH2
    {PB_10,      PWM_2,  STM_PIN_DATA_EXT(STM_MODE_AF_PP, GPIO_NOPULL, GPIO_AF2_TIM2, 3, 0)}, // TIM2_CH3
    {PB_11,      PWM_2,  STM_PIN_DATA_EXT(STM_MODE_AF_PP, GPIO_NOPULL, GPIO_AF2_TIM2, 4, 0)}, // TIM2_CH4
//  {PB_13,      PWM_21, STM_PIN_DATA_EXT(STM_MODE_AF_PP, GPIO_NOPULL, GPIO_AF6_TIM21, 1, 0)}, // TIM21_CH1
//  {PB_14,      PWM_21, STM_PIN_DATA_EXT(STM_MODE_AF_PP, GPIO_NOPULL, GPIO_AF6_TIM21, 2, 0)}, // TIM21_CH2
    {NC, NC, 0}
};

//*** SERIAL ***

MBED_WEAK const PinMap PinMap_UART_TX[] = {
    {PA_2,       UART_2,   STM_PIN_DATA(STM_MODE_AF_PP, GPIO_PULLUP, GPIO_AF4_USART2)},
    {PA_2_ALT0,  LPUART_1, STM_PIN_DATA(STM_MODE_AF_PP, GPIO_PULLUP, GPIO_AF6_LPUART1)},
    {PA_9,       UART_1,   STM_PIN_DATA(STM_MODE_AF_PP, GPIO_PULLUP, GPIO_AF4_USART1)},
    {PA_14,      UART_2,   STM_PIN_DATA(STM_MODE_AF_PP, GPIO_PULLUP, GPIO_AF4_USART2)},
    {PA_14_ALT0, LPUART_1, STM_PIN_DATA(STM_MODE_AF_PP, GPIO_PULLUP, GPIO_AF6_LPUART1)}, // SWCLK
    {PB_6,       UART_1,   STM_PIN_DATA(STM_MODE_AF_PP, GPIO_PULLUP, GPIO_AF0_USART1)},
    {NC,         NC,       0}
};

MBED_WEAK const PinMap PinMap_UART_RX[] = {
    {PA_1,       UART_4,   STM_PIN_DATA(STM_MODE_AF_PP, GPIO_PULLUP, GPIO_AF6_USART4)},
    {PA_3,       UART_2,   STM_PIN_DATA(STM_MODE_AF_PP, GPIO_PULLUP, GPIO_AF4_USART2)},
    {PA_3_ALT0,  LPUART_1, STM_PIN_DATA(STM_MODE_AF_PP, GPIO_PULLUP, GPIO_AF6_LPUART1)},
    {PA_10,      UART_1,   STM_PIN_DATA(STM_MODE_AF_PP, GPIO_PULLUP, GPIO_AF4_USART1)},
    {PA_13,      LPUART_1, STM_PIN_DATA(STM_MODE_AF_PP, GPIO_PULLUP, GPIO_AF6_LPUART1)},  // SWDIO
    {PB_7,       UART_1,   STM_PIN_DATA(STM_MODE_AF_PP, GPIO_PULLUP, GPIO_AF0_USART1)},
    {NC,         NC,       0}
};

MBED_WEAK const PinMap PinMap_UART_RTS[] = {
    {PA_12,      UART_1,   STM_PIN_DATA(STM_MODE_AF_PP, GPIO_PULLUP, GPIO_AF4_USART1)},
    {PB_12,      LPUART_1, STM_PIN_DATA(STM_MODE_AF_PP, GPIO_PULLUP, GPIO_AF4_LPUART1)},
    {PB_14,      LPUART_1, STM_PIN_DATA(STM_MODE_AF_PP, GPIO_PULLUP, GPIO_AF4_LPUART1)},
    {NC,         NC,       0}
};

MBED_WEAK const PinMap PinMap_UART_CTS[] = {
    {PA_0,       UART_2,   STM_PIN_DATA(STM_MODE_AF_PP, GPIO_PULLUP, GPIO_AF4_USART2)},
    {PA_11,      UART_1,   STM_PIN_DATA(STM_MODE_AF_PP, GPIO_PULLUP, GPIO_AF4_USART1)},
    {PB_13,      LPUART_1, STM_PIN_DATA(STM_MODE_AF_PP, GPIO_PULLUP, GPIO_AF4_LPUART1)},
    {NC,         NC,       0}
};

//*** SPI ***

MBED_WEAK const PinMap PinMap_SPI_MOSI[] = {
    {PA_7,       SPI_1, STM_PIN_DATA(STM_MODE_AF_PP, GPIO_NOPULL, GPIO_AF0_SPI1)},
    {PA_12,      SPI_1, STM_PIN_DATA(STM_MODE_AF_PP, GPIO_NOPULL, GPIO_AF0_SPI1)},
    {PB_5,       SPI_1, STM_PIN_DATA(STM_MODE_AF_PP, GPIO_NOPULL, GPIO_AF0_SPI1)},
    {PB_15,      SPI_2, STM_PIN_DATA(STM_MODE_AF_PP, GPIO_NOPULL, GPIO_AF0_SPI2)},
    {NC, NC, 0}
};

MBED_WEAK const PinMap PinMap_SPI_MISO[] = {
    {PA_6,       SPI_1, STM_PIN_DATA(STM_MODE_AF_PP, GPIO_NOPULL, GPIO_AF0_SPI1)},
    {PA_11,      SPI_1, STM_PIN_DATA(STM_MODE_AF_PP, GPIO_NOPULL, GPIO_AF0_SPI1)},
    {PB_4,       SPI_1, STM_PIN_DATA(STM_MODE_AF_PP, GPIO_NOPULL, GPIO_AF0_SPI1)},
    {PB_14,      SPI_2, STM_PIN_DATA(STM_MODE_AF_PP, GPIO_NOPULL, GPIO_AF0_SPI2)},
    {NC, NC, 0}
};

MBED_WEAK const PinMap PinMap_SPI_SCLK[] = {
    {PA_5,       SPI_1, STM_PIN_DATA(STM_MODE_AF_PP, GPIO_NOPULL, GPIO_AF0_SPI1)},
    {PB_3,       SPI_1, STM_PIN_DATA(STM_MODE_AF_PP, GPIO_NOPULL, GPIO_AF0_SPI1)},
    {PB_10,      SPI_2, STM_PIN_DATA(STM_MODE_AF_PP, GPIO_NOPULL, GPIO_AF5_SPI2)},
    {PB_13,      SPI_2, STM_PIN_DATA(STM_MODE_AF_PP, GPIO_NOPULL, GPIO_AF0_SPI2)},
    {NC, NC, 0}
};

MBED_WEAK const PinMap PinMap_SPI_SSEL[] = {
    {PA_4,       SPI_1, STM_PIN_DATA(STM_MODE_AF_PP, GPIO_NOPULL, GPIO_AF0_SPI1)},
    {PA_15,      SPI_1, STM_PIN_DATA(STM_MODE_AF_PP, GPIO_NOPULL, GPIO_AF0_SPI1)},
    {PB_9,       SPI_2, STM_PIN_DATA(STM_MODE_AF_PP, GPIO_NOPULL, GPIO_AF5_SPI2)},
    {PB_12,      SPI_2, STM_PIN_DATA(STM_MODE_AF_PP, GPIO_NOPULL, GPIO_AF0_SPI2)},
    {NC, NC, 0}
};

//*** USBDEVICE ***

MBED_WEAK const PinMap PinMap_USB_FS[] = {
    {PA_11,     USB_FS, STM_PIN_DATA(STM_MODE_INPUT, GPIO_NOPULL, GPIO_AF_NONE)}, // USB_DM
    {PA_12,     USB_FS, STM_PIN_DATA(STM_MODE_INPUT, GPIO_NOPULL, GPIO_AF_NONE)}, // USB_DP
//  {PA_13,     USB_FS, STM_PIN_DATA(STM_MODE_AF_PP, GPIO_PULLUP, GPIO_AF2_USB)}, // USB_NOE
    {NC, NC, 0}
};
