Mircerson/AERQ/Code/v1/stm32customtargets/TARGET_STM32F4/TARGET_CORE2/system_clock.c

/* mbed Microcontroller Library
 * SPDX-License-Identifier: BSD-3-Clause
 ******************************************************************************
 *
 * Copyright (c) 2015-2021 STMicroelectronics.
 * All rights reserved.
 *
 * This software component is licensed by ST under BSD 3-Clause license,
 * the "License"; You may not use this file except in compliance with the
 * License. You may obtain a copy of the License at:
 *                        opensource.org/licenses/BSD-3-Clause
 *
 ******************************************************************************
 */

/**
  * This file configures the system clock as follows:
  *-----------------------------------------------------------------------------
  * System clock source                | 1- PLL_HSE_EXTC        | 3- PLL_HSI
  *                                    | (external 8 MHz clock) | (internal 16 MHz)
  *                                    | 2- PLL_HSE_XTAL        |
  *                                    | (external 8 MHz xtal)  |
  *-----------------------------------------------------------------------------
  * SYSCLK(MHz)                        | 168                    | 168
  *-----------------------------------------------------------------------------
  * AHBCLK (MHz)                       | 168                    | 168
  *-----------------------------------------------------------------------------
  * APB1CLK (MHz)                      | 42                     | 42
  *-----------------------------------------------------------------------------
  * APB2CLK (MHz)                      | 84                     | 84
  *-----------------------------------------------------------------------------
  * USB capable (48 MHz precise clock) | YES                    | NO
  *-----------------------------------------------------------------------------
**/

#include "stm32f4xx.h"
#include "mbed_error.h"

// clock source is selected with CLOCK_SOURCE in json config
#define USE_PLL_HSE_EXTC     0x8  // Use external clock (ST Link MCO)
#define USE_PLL_HSE_XTAL     0x4  // Use external xtal (X3 on board - not provided by default)
#define USE_PLL_HSI          0x2  // Use HSI internal clock

#ifndef CLOCK_CONFIG_ADV       // enable settings for Mbed Os 5.14
    #define CLOCK_CONFIG_ADV 0 
#endif /* CLOCK_CONFIG_ADV */  

#if ( ((CLOCK_SOURCE) & USE_PLL_HSE_XTAL) || ((CLOCK_SOURCE) & USE_PLL_HSE_EXTC) )
uint8_t SetSysClock_PLL_HSE(uint8_t bypass);
#endif /* ((CLOCK_SOURCE) & USE_PLL_HSE_XTAL) || ((CLOCK_SOURCE) & USE_PLL_HSE_EXTC) */

#if ((CLOCK_SOURCE) & USE_PLL_HSI)
uint8_t SetSysClock_PLL_HSI(void);
#endif /* ((CLOCK_SOURCE) & USE_PLL_HSI) */

/**
  * @brief  Setup the microcontroller system
  *         Initialize the FPU setting, vector table location and External memory 
  *         configuration.
  * @param  None
  * @retval None
  */
void SystemInit(void)
{
#include "nvic_addr.h"                   // MBED
  SCB->VTOR = NVIC_FLASH_VECTOR_ADDRESS; // MBED

  /* FPU settings ------------------------------------------------------------*/
  #if (__FPU_PRESENT == 1) && (__FPU_USED == 1)
    SCB->CPACR |= ((3UL << 10*2)|(3UL << 11*2));  /* set CP10 and CP11 Full Access */
  #endif

#if (CLOCK_CONFIG_ADV == 1)
    /* Reset the RCC clock configuration to the default reset state ------------*/
    /* Set HSION bit */
    RCC->CR |= (uint32_t)0x00000001;

    /* Reset CFGR register */
    RCC->CFGR = 0x00000000;

    /* Reset HSEON, CSSON and PLLON bits */
    RCC->CR &= (uint32_t)0xFEF6FFFF;

    /* Reset PLLCFGR register */
    RCC->PLLCFGR = 0x24003010;

    /* Reset HSEBYP bit */
    RCC->CR &= (uint32_t)0xFFFBFFFF;

    /* Disable all interrupts */
    RCC->CIR = 0x00000000;
#endif /* CLOCK_CONFIG_ADV */

#if defined (DATA_IN_ExtSRAM) || defined (DATA_IN_ExtSDRAM)
  SystemInit_ExtMemCtl(); 
#endif /* DATA_IN_ExtSRAM || DATA_IN_ExtSDRAM */

  /* Configure the Vector Table location -------------------------------------*/
#if defined(USER_VECT_TAB_ADDRESS)
  SCB->VTOR = VECT_TAB_BASE_ADDRESS | VECT_TAB_OFFSET; /* Vector Table Relocation in Internal SRAM */
#endif /* USER_VECT_TAB_ADDRESS */
}

/**
  * @brief  Configures the System clock source, PLL Multiplier and Divider factors,
  *               AHB/APBx prescalers and Flash settings
  * @note   This function should be called only once the RCC clock configuration
  *         is reset to the default reset state (done in SystemInit() function).
  * @param  None
  * @retval None
  */

MBED_WEAK void SetSysClock(void)
{
#if ((CLOCK_SOURCE) & USE_PLL_HSE_EXTC)
    /* 1- Try to start with HSE and external clock */
    if (SetSysClock_PLL_HSE(1) == 0)
#endif
    {
#if ((CLOCK_SOURCE) & USE_PLL_HSE_XTAL)
        /* 2- If fail try to start with HSE and external xtal */
        if (SetSysClock_PLL_HSE(0) == 0)
#endif
        {
#if ((CLOCK_SOURCE) & USE_PLL_HSI)
            /* 3- If fail start with HSI clock */
            if (SetSysClock_PLL_HSI() == 0)
#endif
            {
                {
                    error("SetSysClock failed\n");
                }
            }
        }
    }
}

#if ( ((CLOCK_SOURCE) & USE_PLL_HSE_XTAL) || ((CLOCK_SOURCE) & USE_PLL_HSE_EXTC) )
/******************************************************************************/
/*            PLL (clocked by HSE) used as System clock source                */
/******************************************************************************/
uint8_t SetSysClock_PLL_HSE(uint8_t bypass)
{
    RCC_OscInitTypeDef RCC_OscInitStruct = {0};
    RCC_ClkInitTypeDef RCC_ClkInitStruct = {0};

    /* The voltage scaling allows optimizing the power consumption when the device is
       clocked below the maximum system frequency, to update the voltage scaling value
       regarding system frequency refer to product datasheet. */
    __HAL_RCC_PWR_CLK_ENABLE();
    __HAL_PWR_VOLTAGESCALING_CONFIG(PWR_REGULATOR_VOLTAGE_SCALE1);

    /* Enable HSE oscillator and activate PLL with HSE as source */
    RCC_OscInitStruct.OscillatorType      = RCC_OSCILLATORTYPE_HSE;
    if (bypass == 0) {
        RCC_OscInitStruct.HSEState          = RCC_HSE_ON; /* External 8 MHz xtal on OSC_IN/OSC_OUT */
    } else {
        RCC_OscInitStruct.HSEState          = RCC_HSE_BYPASS; /* External 8 MHz clock on OSC_IN */
    }
    RCC_OscInitStruct.HSIState            = RCC_HSI_OFF;
    RCC_OscInitStruct.PLL.PLLState        = RCC_PLL_ON;
    RCC_OscInitStruct.PLL.PLLSource       = RCC_PLLSOURCE_HSE;
    RCC_OscInitStruct.PLL.PLLM            = 8;             // VCO input clock = 1 MHz (8 MHz / 8)
    RCC_OscInitStruct.PLL.PLLN            = 336;           // VCO output clock = 336 MHz (1 MHz * 336)
    RCC_OscInitStruct.PLL.PLLP            = RCC_PLLP_DIV2; // PLLCLK = 168 MHz (336 MHz / 2)
    RCC_OscInitStruct.PLL.PLLQ            = 7;             // USB clock = 48 MHz (336 MHz / 7) --> OK for USB
    if (HAL_RCC_OscConfig(&RCC_OscInitStruct) != HAL_OK) {
        return 0; // FAIL
    }

    /* Select PLL as system clock source and configure the HCLK, PCLK1 and PCLK2 clocks dividers */
    RCC_ClkInitStruct.ClockType      = (RCC_CLOCKTYPE_SYSCLK | RCC_CLOCKTYPE_HCLK | RCC_CLOCKTYPE_PCLK1 | RCC_CLOCKTYPE_PCLK2);
    RCC_ClkInitStruct.SYSCLKSource   = RCC_SYSCLKSOURCE_PLLCLK; // 168 MHz
    RCC_ClkInitStruct.AHBCLKDivider  = RCC_SYSCLK_DIV1; // 168 MHz
    RCC_ClkInitStruct.APB1CLKDivider = RCC_HCLK_DIV4;   // 42 MHz
    RCC_ClkInitStruct.APB2CLKDivider = RCC_HCLK_DIV2;   // 84 MHz (SPI1 clock...)
    if (HAL_RCC_ClockConfig(&RCC_ClkInitStruct, FLASH_LATENCY_5) != HAL_OK) {
        return 0; // FAIL
    }

    /* Output clock on MCO1 pin(PA8) for debugging purpose */
    /*
    if (bypass == 0)
      HAL_RCC_MCOConfig(RCC_MCO1, RCC_MCO1SOURCE_HSE, RCC_MCODIV_2); // 4 MHz
    else
      HAL_RCC_MCOConfig(RCC_MCO1, RCC_MCO1SOURCE_HSE, RCC_MCODIV_1); // 8 MHz
    */

    return 1; // OK
}
#endif /* ((CLOCK_SOURCE) & USE_PLL_HSE_XTAL) || ((CLOCK_SOURCE) & USE_PLL_HSE_EXTC) */

#if ((CLOCK_SOURCE) & USE_PLL_HSI)
/******************************************************************************/
/*            PLL (clocked by HSI) used as System clock source                */
/******************************************************************************/
uint8_t SetSysClock_PLL_HSI(void)
{
    RCC_OscInitTypeDef RCC_OscInitStruct;
    RCC_ClkInitTypeDef RCC_ClkInitStruct;

    /* The voltage scaling allows optimizing the power consumption when the device is
       clocked below the maximum system frequency, to update the voltage scaling value
       regarding system frequency refer to product datasheet. */
    __HAL_RCC_PWR_CLK_ENABLE();
    __HAL_PWR_VOLTAGESCALING_CONFIG(PWR_REGULATOR_VOLTAGE_SCALE1);

    /* Enable HSI oscillator and activate PLL with HSI as source */
    RCC_OscInitStruct.OscillatorType      = RCC_OSCILLATORTYPE_HSI | RCC_OSCILLATORTYPE_HSE;
    RCC_OscInitStruct.HSIState            = RCC_HSI_ON;
    RCC_OscInitStruct.HSEState            = RCC_HSE_OFF;
    RCC_OscInitStruct.HSICalibrationValue = RCC_HSICALIBRATION_DEFAULT;
    RCC_OscInitStruct.PLL.PLLState        = RCC_PLL_ON;
    RCC_OscInitStruct.PLL.PLLSource       = RCC_PLLSOURCE_HSI;
    RCC_OscInitStruct.PLL.PLLM            = 16;            // VCO input clock = 1 MHz (16 MHz / 16)
    RCC_OscInitStruct.PLL.PLLN            = 336;           // VCO output clock = 336 MHz (1 MHz * 336)
    RCC_OscInitStruct.PLL.PLLP            = RCC_PLLP_DIV2; // PLLCLK = 168 MHz (336 MHz / 2)
    RCC_OscInitStruct.PLL.PLLQ            = 7;             // USB clock = 48 MHz (336 MHz / 7) --> freq is ok but not precise enough
    if (HAL_RCC_OscConfig(&RCC_OscInitStruct) != HAL_OK) {
        return 0; // FAIL
    }

    /* Select PLL as system clock source and configure the HCLK, PCLK1 and PCLK2 clocks dividers */
    RCC_ClkInitStruct.ClockType      = (RCC_CLOCKTYPE_SYSCLK | RCC_CLOCKTYPE_HCLK | RCC_CLOCKTYPE_PCLK1 | RCC_CLOCKTYPE_PCLK2);
    RCC_ClkInitStruct.SYSCLKSource   = RCC_SYSCLKSOURCE_PLLCLK; // 168 MHz
    RCC_ClkInitStruct.AHBCLKDivider  = RCC_SYSCLK_DIV1;         // 168 MHz
    RCC_ClkInitStruct.APB1CLKDivider = RCC_HCLK_DIV4;           // 42 MHz
    RCC_ClkInitStruct.APB2CLKDivider = RCC_HCLK_DIV2;           // 84 MHz
    if (HAL_RCC_ClockConfig(&RCC_ClkInitStruct, FLASH_LATENCY_5) != HAL_OK) {
        return 0; // FAIL
    }

    /* Output clock on MCO1 pin(PA8) for debugging purpose */
    //HAL_RCC_MCOConfig(RCC_MCO1, RCC_MCO1SOURCE_HSI, RCC_MCODIV_1); // 16 MHz

    return 1; // OK
}
#endif /* ((CLOCK_SOURCE) & USE_PLL_HSI) */
